Zille9/Hive-Max-Retrostyle-Computer/Pictures/IMG_0248.JPG

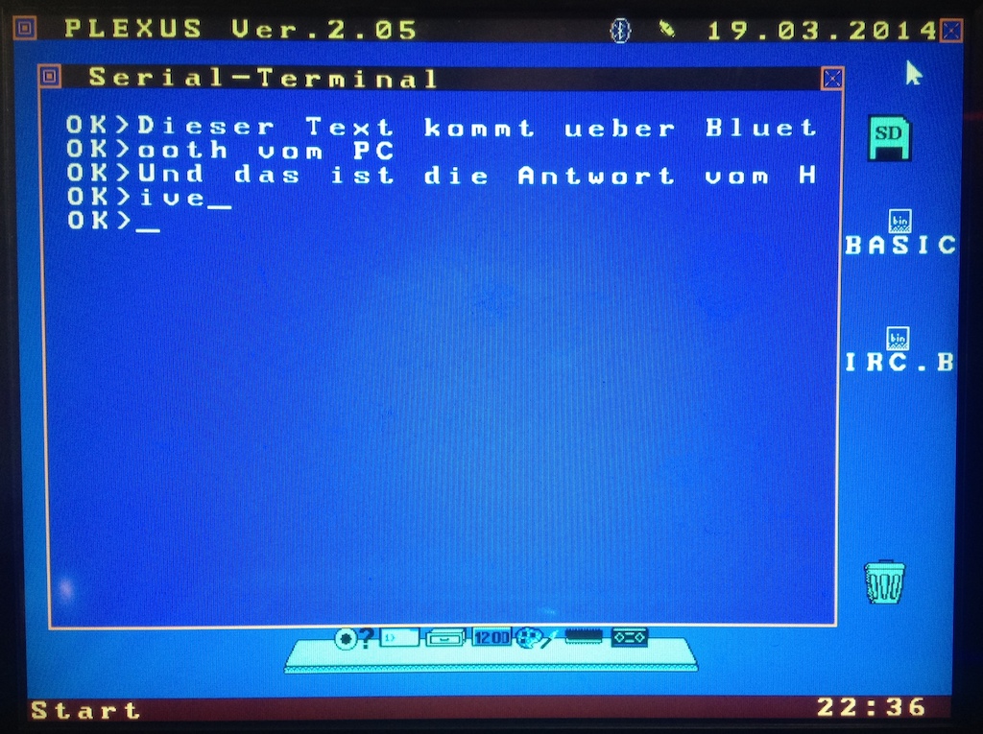
Pictures/IMG_0248.JPG
