Zille9/Hive-Max-Retrostyle-Computer/Pictures/IMG_0555_1.JPG

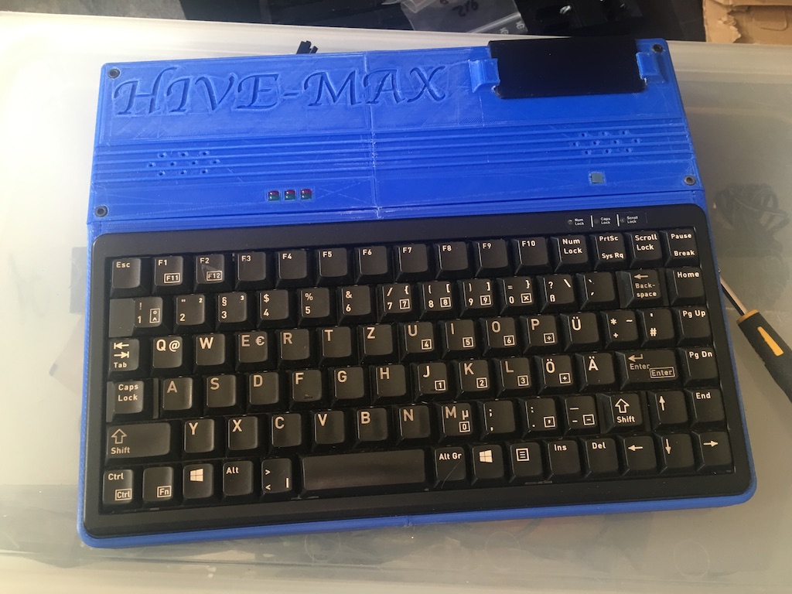
Pictures/IMG_0555_1.JPG
