Zille9/Hive-Max-Retrostyle-Computer/Pictures/IMG_0564_1.JPG

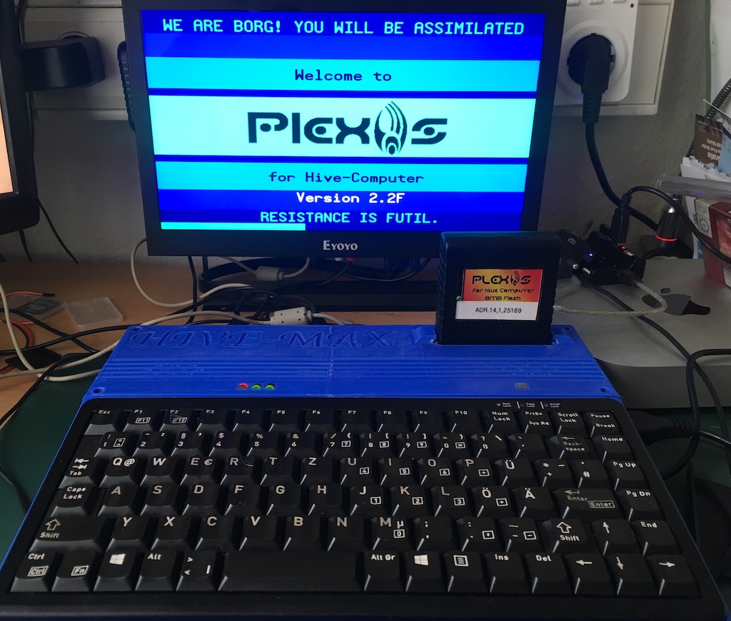
Pictures/IMG_0564_1.JPG
