Zille9/Hive-Max-Retrostyle-Computer/Pictures/IMG_0597.JPG

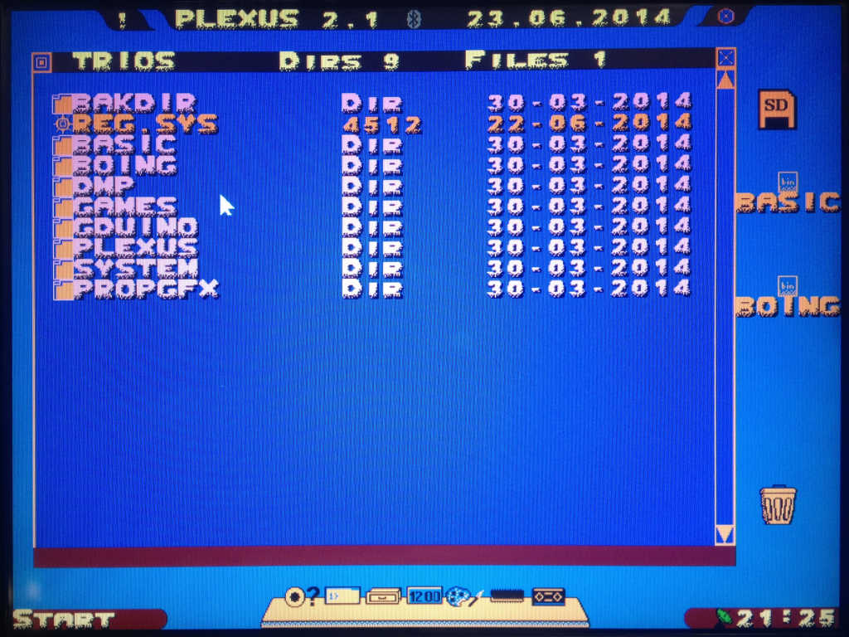
Pictures/IMG_0597.JPG
